psrobotics/Bhaptic_desktop/pic/1050177-01.jpeg

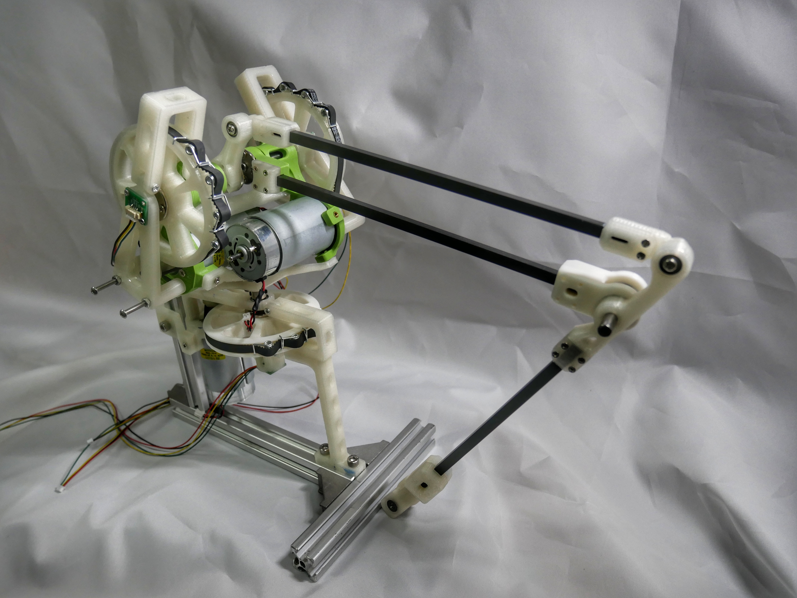
pic/1050177-01.jpeg
