psrobotics/Bhaptic_desktop/pic/depth.JPG

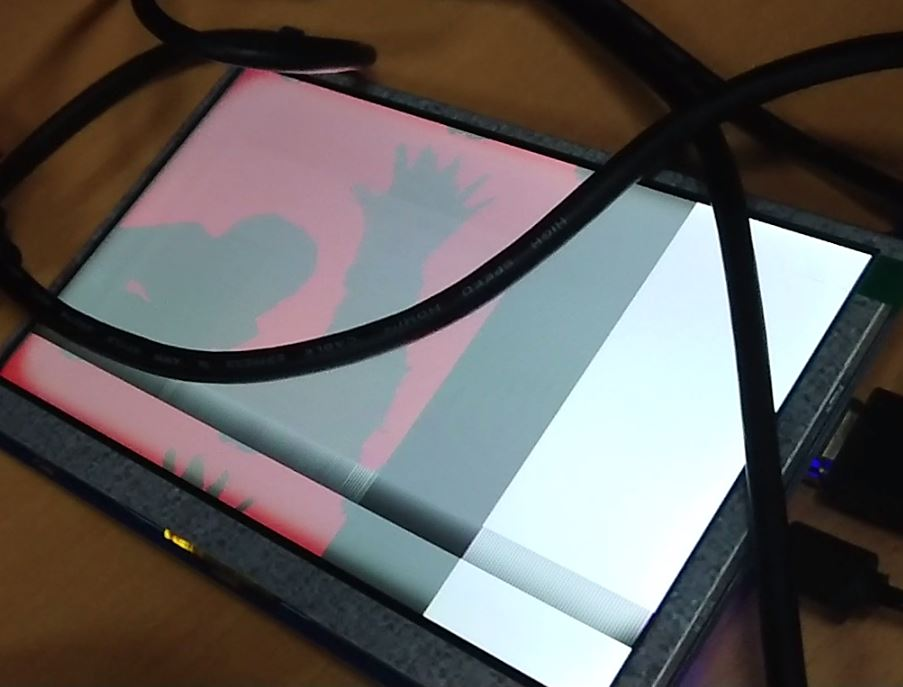
pic/depth.JPG
