psrobotics/Bhaptic_desktop/pic/docu/0001.jpg

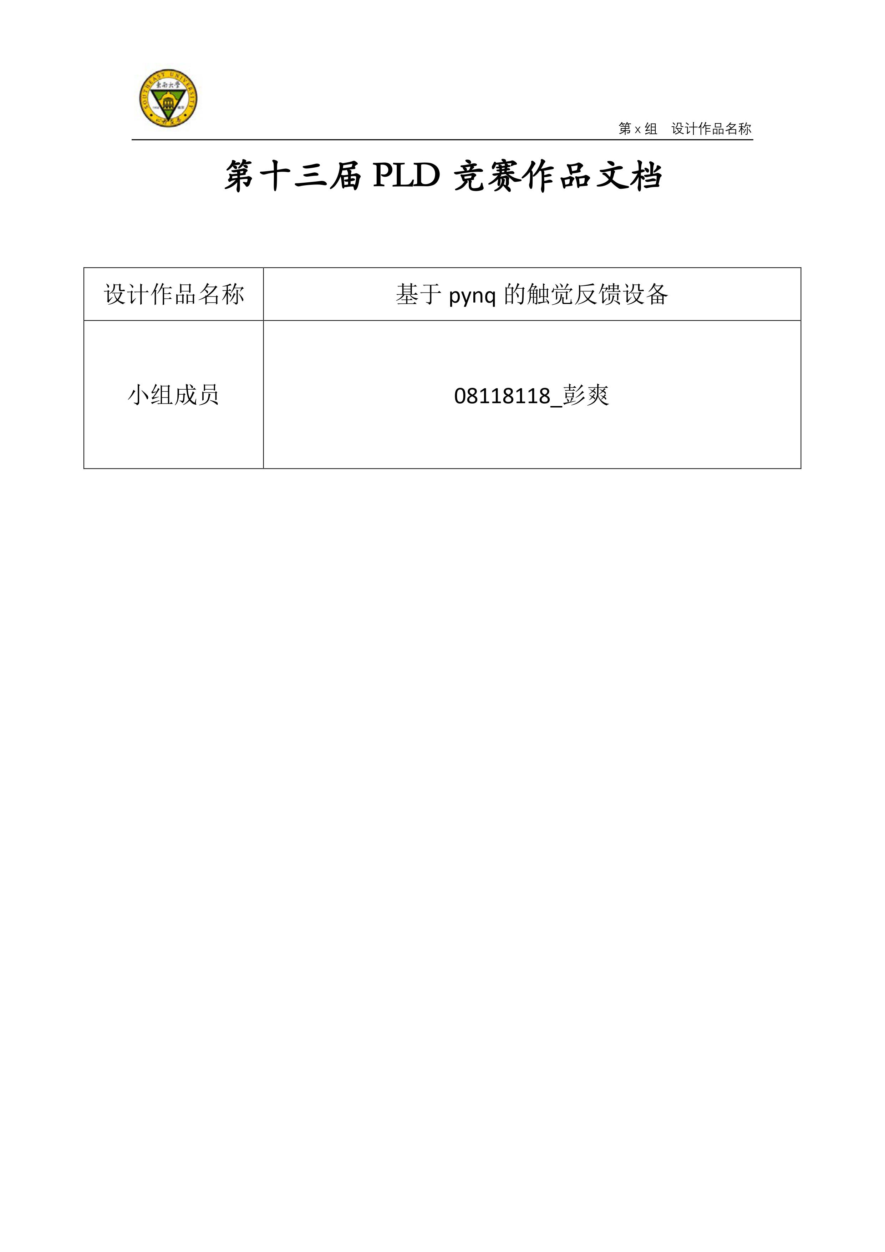
pic/docu/0001.jpg
