psrobotics/Bhaptic_desktop/pic/DRV.JPG

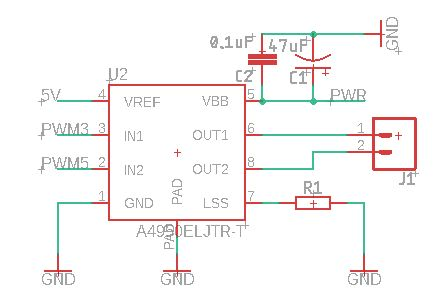
pic/DRV.JPG
