psrobotics/Bhaptic_desktop/hardware/gt2-pulley-120-tooth-1.snapshot.1/120teeth gt2 pulley.SLDPRT

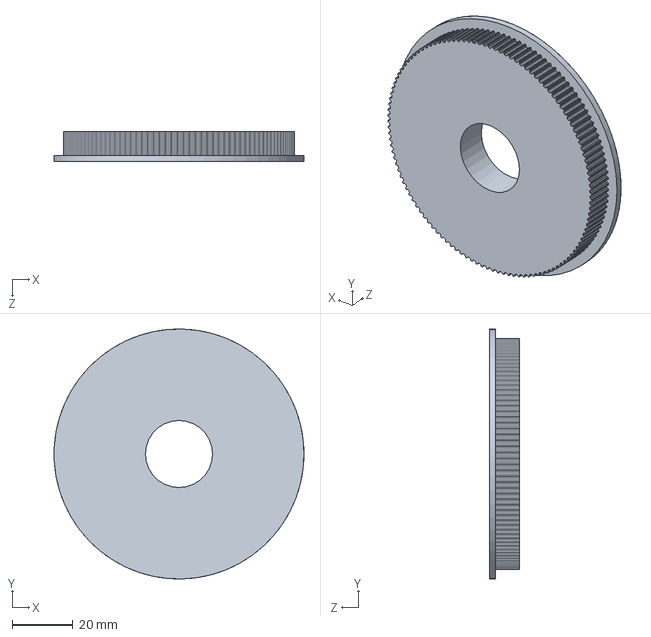
[picture p36: CAD file, 2024-03-05]
hardware/gt2-pulley-120-tooth-1.snapshot.1/120teeth gt2 pulley.SLDPRT
82.0 x 82.0 x 10.0 mm
