psrobotics/Bhaptic_desktop/hardware/export_20190921/arm_linkage_2_mod.stl

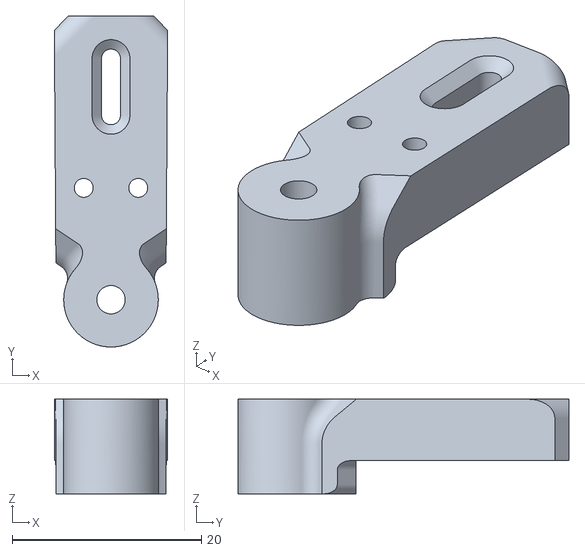
[picture p37: CAD file, 2024-03-05]
hardware/export_20190921/arm_linkage_2_mod.stl
12.0 x 35.0 x 10.0
