psrobotics/Bhaptic_desktop/hardware/export_20191015/arm_frame_3.stl

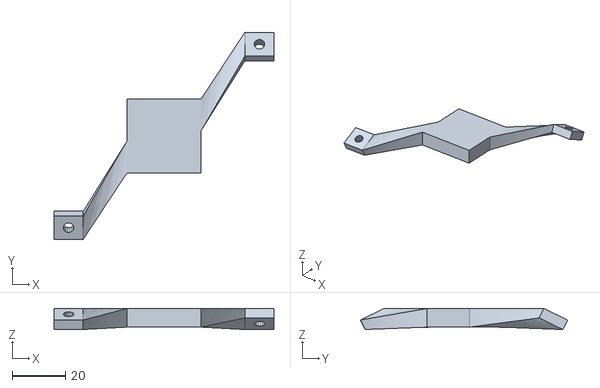
[picture p38: CAD file, 2024-03-05]
hardware/export_20191015/arm_frame_3.stl
83.0 x 78.2 x 7.98
