psrobotics/Bhaptic_desktop/hardware/export_20191017/frame-1.stl

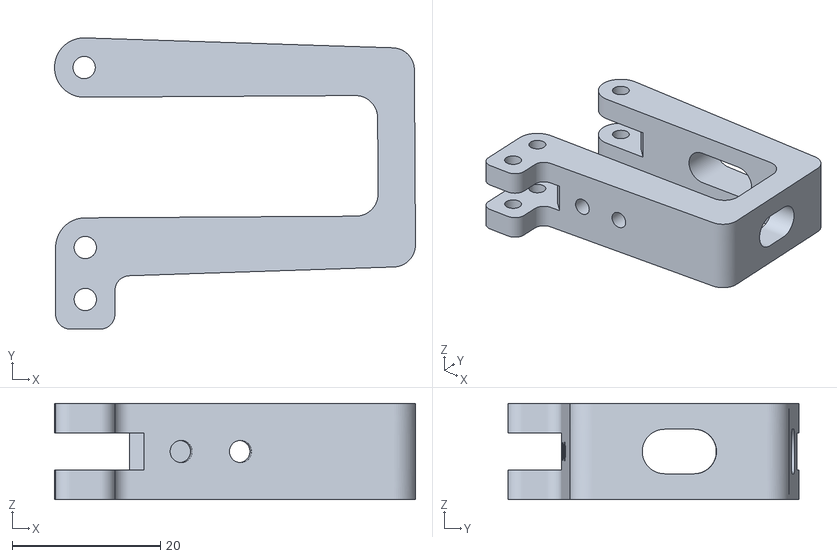
[picture p39: CAD file, 2024-03-05]
hardware/export_20191017/frame-1.stl
48.6 x 39.2 x 13.0
