psrobotics/Bhaptic_desktop/hardware/export_20191022/armtip_2_mod.stl

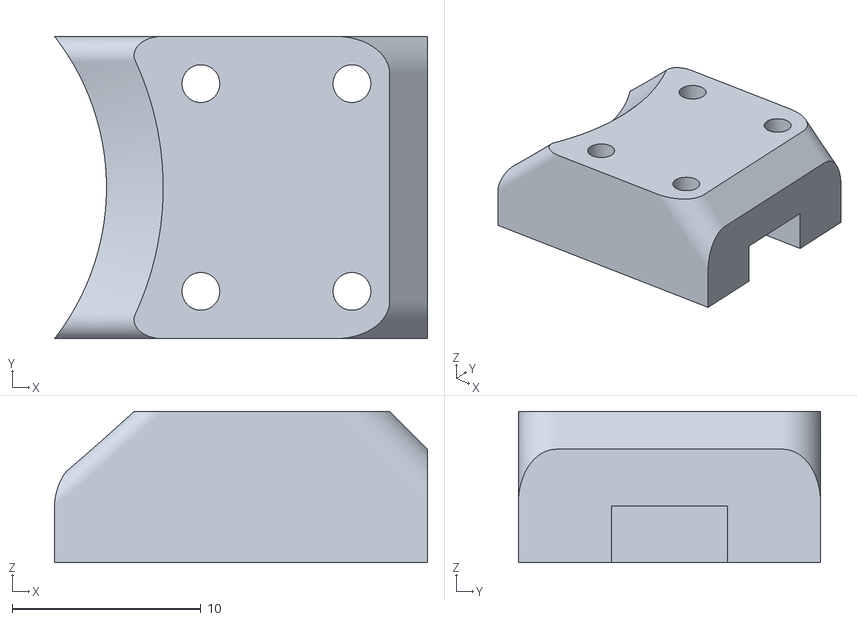
[picture p41: CAD file, 2024-03-05]
hardware/export_20191022/armtip_2_mod.stl
19.8 x 16.0 x 8.00
