psrobotics/Bhaptic_desktop/hardware/export_20191028/end_tip_2.stl

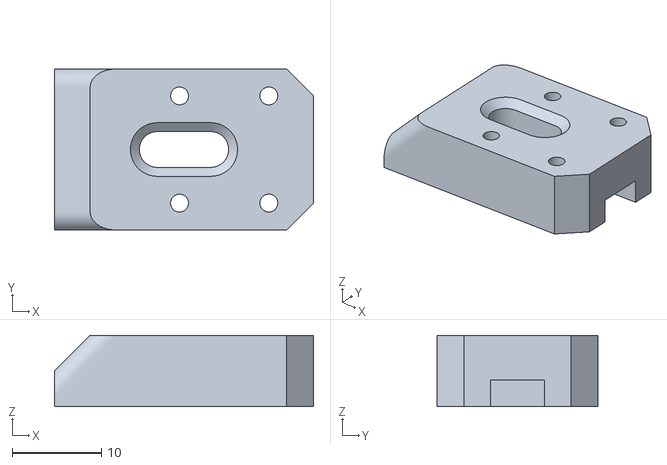
[picture p42: CAD file, 2024-03-05]
hardware/export_20191028/end_tip_2.stl
29.0 x 18.0 x 8.00
