psrobotics/Bhaptic_desktop/hardware/export_20191105/pen_1.stl

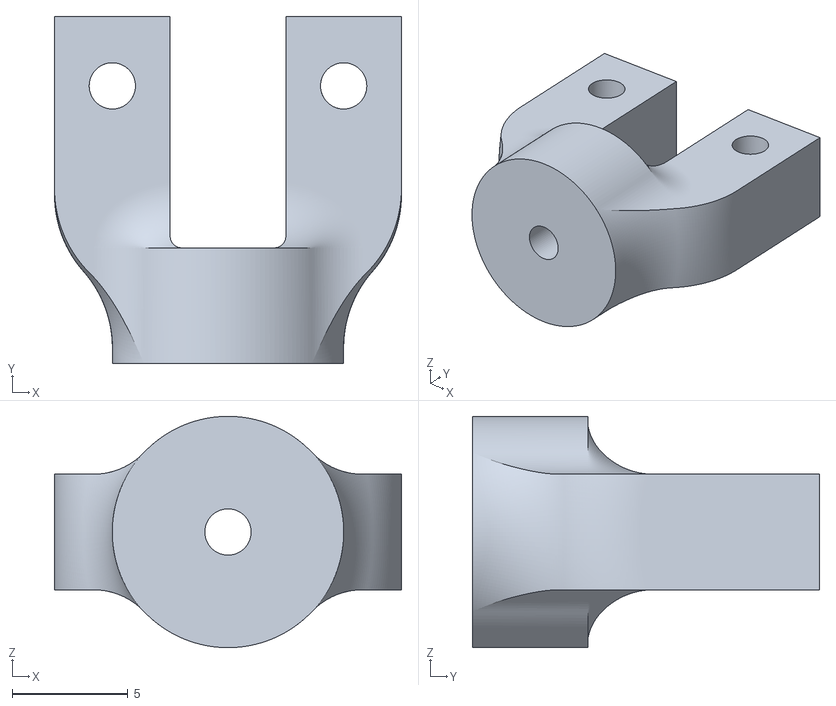
[picture p43: CAD file, 2024-03-05]
hardware/export_20191105/pen_1.stl
15.0 x 15.0 x 10.00
