psrobotics/Bhaptic_desktop/hardware/export_20191223/2200_support_3.stl

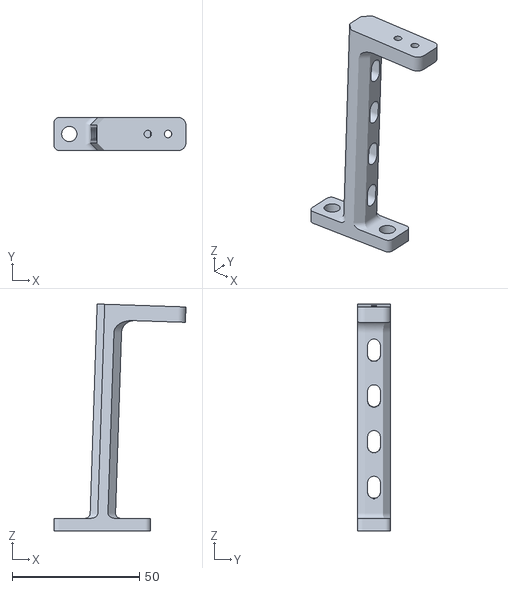
[picture p44: CAD file, 2024-03-05]
hardware/export_20191223/2200_support_3.stl
51.9 x 13.0 x 89.4
