psrobotics/Bhaptic_desktop/hardware/export_20191015/motor_holder_1_mod.stl

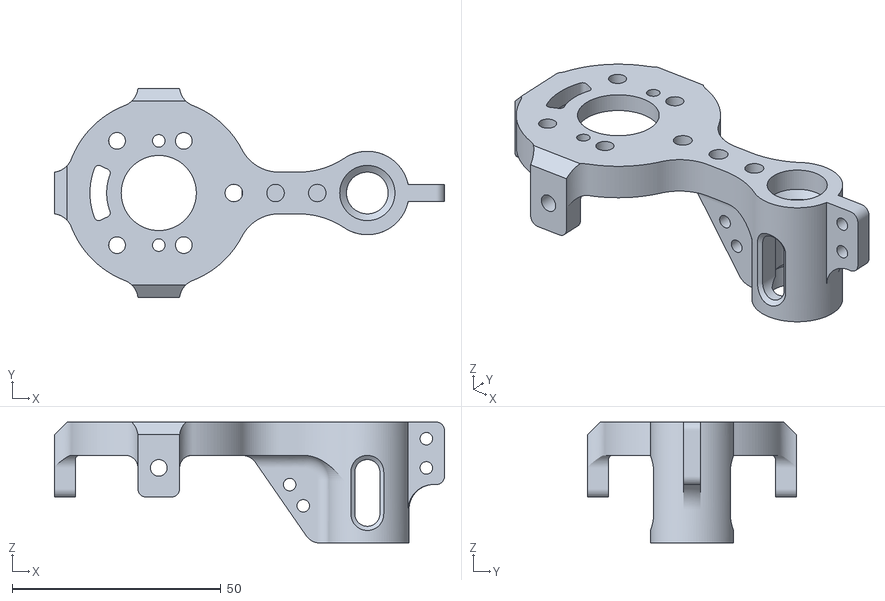
[picture p45: CAD file, 2024-03-05]
hardware/export_20191015/motor_holder_1_mod.stl
93.5 x 50.0 x 29.0
