psrobotics/Bhaptic_desktop/hardware/export_20191018/arm_frame_1.stl

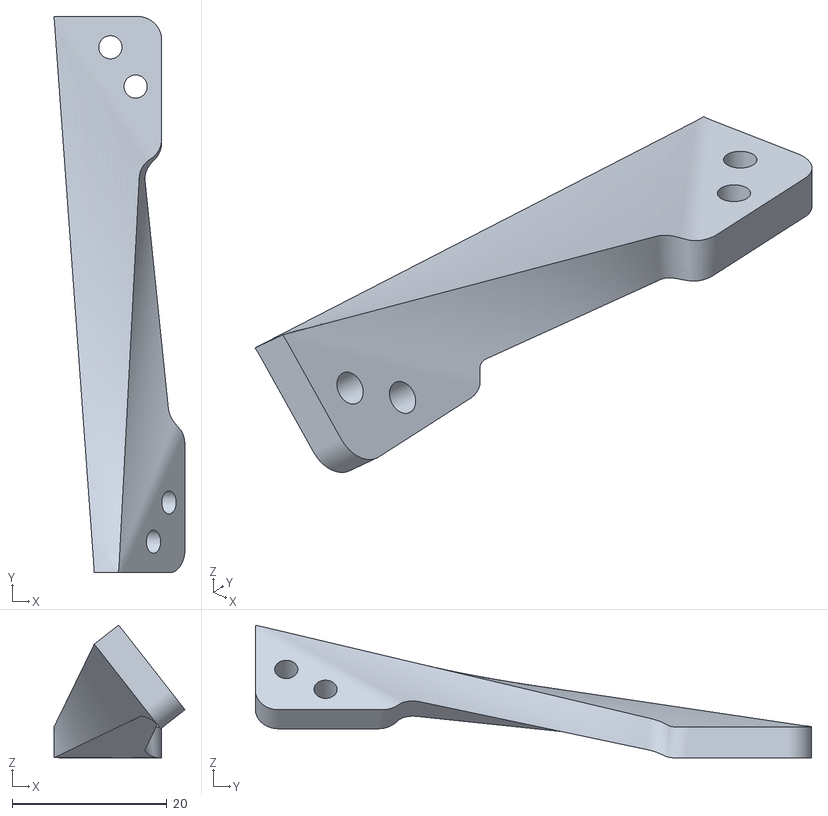
[picture p46: CAD file, 2024-03-05]
hardware/export_20191018/arm_frame_1.stl
17.0 x 72.0 x 17.2
