psrobotics/Bhaptic_desktop/hardware/export_20191028/end_tip_1.stl

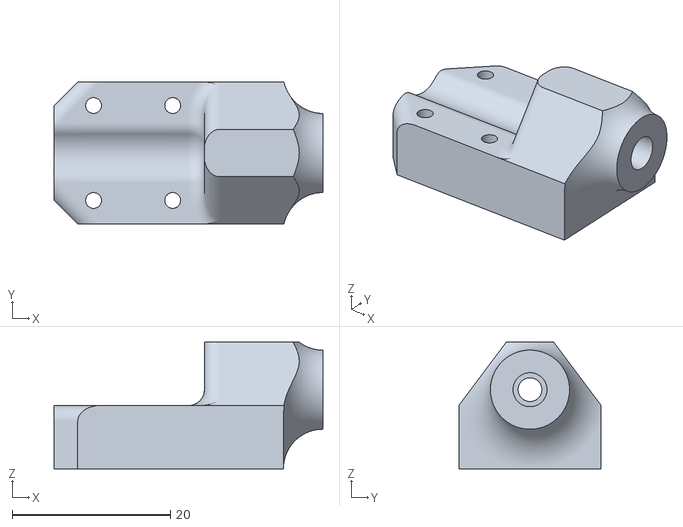
[picture p47: CAD file, 2024-03-05]
hardware/export_20191028/end_tip_1.stl
34.0 x 18.0 x 16.0
