psrobotics/Bhaptic_desktop/hardware/export_20191223/2020_fixer_1.stl

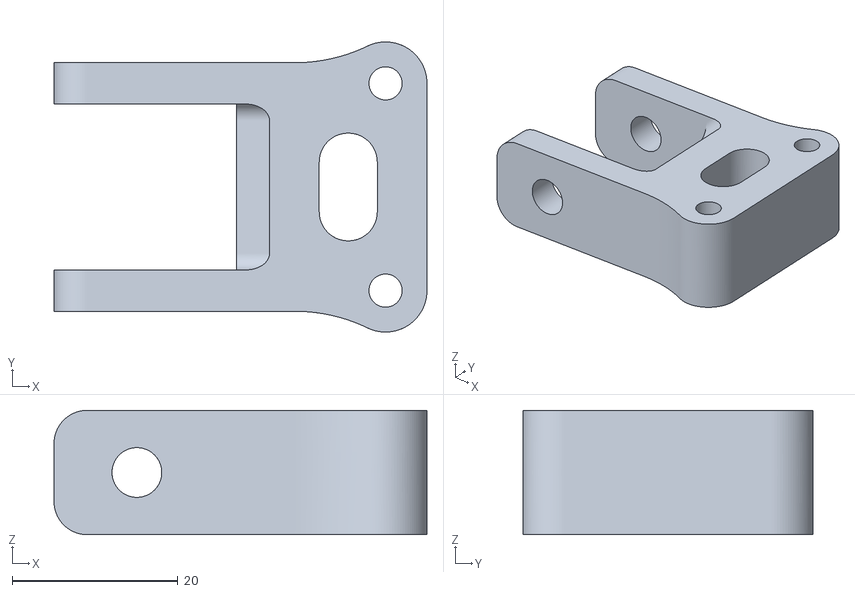
[picture p48: CAD file, 2024-03-05]
hardware/export_20191223/2020_fixer_1.stl
45.0 x 35.0 x 15.0
