psrobotics/Bhaptic_desktop/hardware/export_20191015/120teeth gt2 pulley.stl

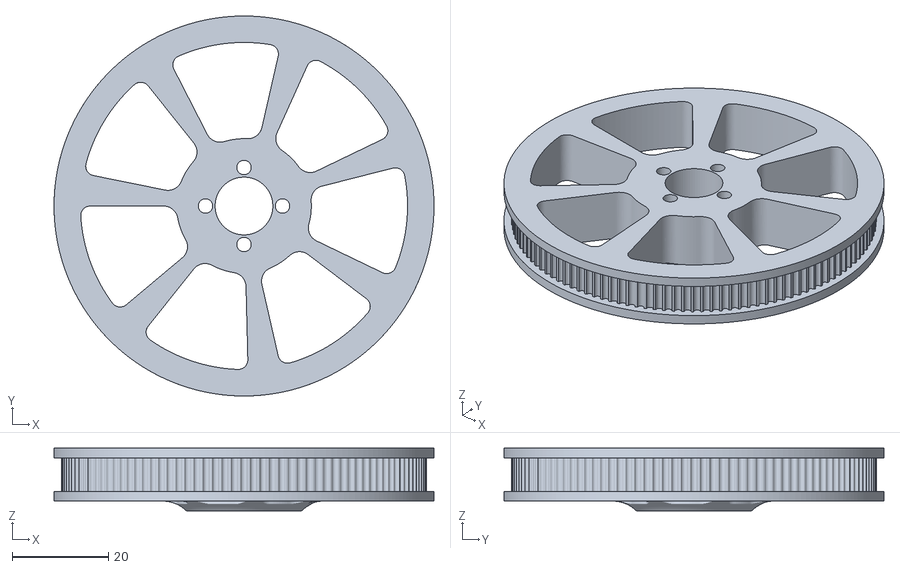
[picture p49: CAD file, 2024-03-05]
hardware/export_20191015/120teeth gt2 pulley.stl
79.0 x 79.0 x 13.0
