psrobotics/Bhaptic_desktop/hardware/export_20191018/arm_frame_2.stl

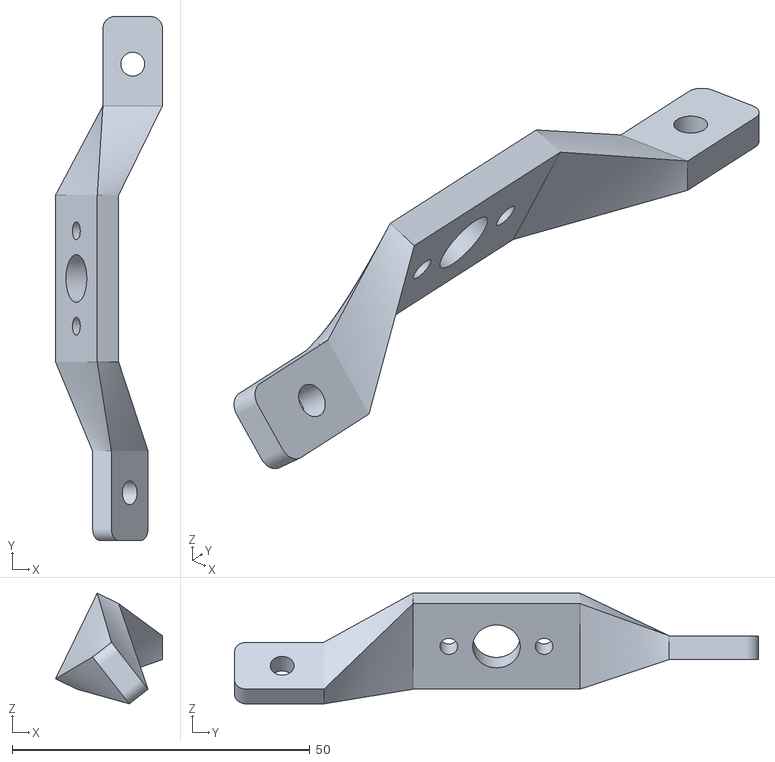
[picture p50: CAD file, 2024-03-05]
hardware/export_20191018/arm_frame_2.stl
18.0 x 88.0 x 18.6
