psrobotics/Bhaptic_desktop/hardware/export_20190921/arm_linkage_3_mod.stl

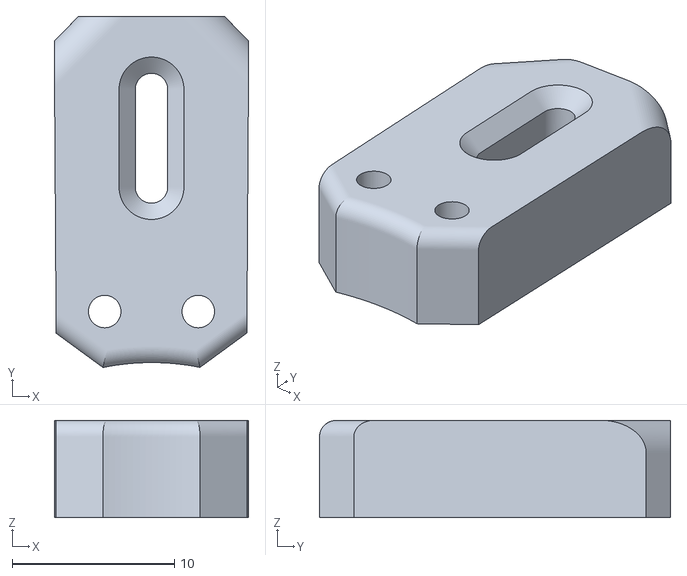
[picture p51: CAD file, 2024-03-05]
hardware/export_20190921/arm_linkage_3_mod.stl
12.0 x 21.6 x 6.00
