psrobotics/Bhaptic_desktop/hardware/export_20191015/armtip_1.stl

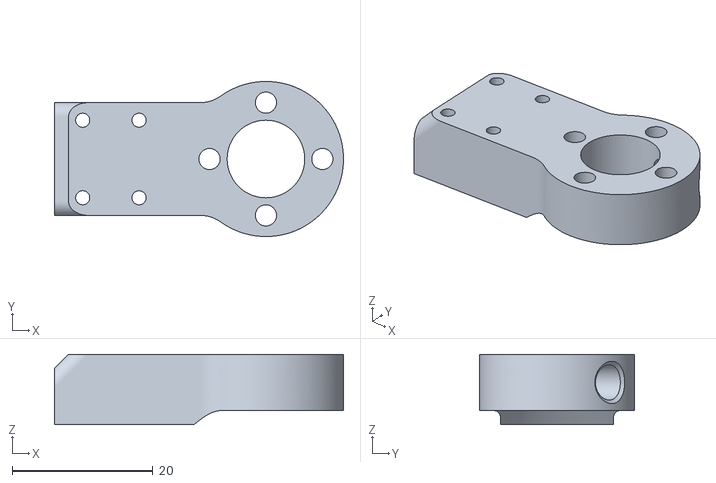
[picture p52: CAD file, 2024-03-05]
hardware/export_20191015/armtip_1.stl
41.0 x 22.0 x 10.0
